zlosynth/proton/eurorack/src/system/randomizer.rs

use hal::prelude::_stm32h7xx_hal_rng_RngCore;
use hal::rng::Rng;
use stm32h7xx_hal as hal;

use proton_instruments_interface::Rand;

pub struct Randomizer {
    pub rng: Rng,
}

impl Randomizer {
    pub fn new(rng: Rng) -> Self {
        Self { rng }
    }
}

impl Rand for Randomizer {
    fn generate(&mut self) -> u16 {
        self.rng.gen().unwrap()
    }
}
