zlosynth/proton/control/src/output_request.rs

#[derive(Clone, Copy, Debug)]
#[cfg_attr(feature = "defmt", derive(defmt::Format))]
pub struct OutputRequest {
    pub gate: [Gate; 3],
    pub cv: [Cv; 2],
}

#[derive(Clone, Copy, Debug)]
#[cfg_attr(feature = "defmt", derive(defmt::Format))]
pub struct Gate {
    pub value: bool,
}

#[derive(Clone, Copy, Debug)]
#[cfg_attr(feature = "defmt", derive(defmt::Format))]
pub struct Cv {
    pub value: f32,
}
