zlosynth/proton/control/src/input_snapshot.rs

#[derive(Clone, Copy, Debug)]
#[cfg_attr(feature = "defmt", derive(defmt::Format))]
pub struct InputSnapshot {
    pub pot: Pot,
    pub cv: [Cv; 5],
}

#[derive(Clone, Copy, Debug)]
#[cfg_attr(feature = "defmt", derive(defmt::Format))]
pub struct Pot {
    pub value: f32,
}

#[derive(Clone, Copy, Debug)]
#[cfg_attr(feature = "defmt", derive(defmt::Format))]
pub struct Cv {
    pub value: f32,
}
