zlosynth/proton/ui/examples/display.rs

use core::fmt;
use std::{thread, time::Duration};

use embedded_graphics::{pixelcolor::BinaryColor, prelude::*};
use embedded_graphics_simulator::{
    sdl2::Keycode, OutputSettingsBuilder, SimulatorDisplay, SimulatorEvent, Window,
};

use proton_ui::action::Action;
use proton_ui::display::*;
use proton_ui::reducer;
use proton_ui::state::*;

fn speed_writter(destination: &mut dyn fmt::Write, value: f32) {
    write!(destination, "{:.2}%", value).unwrap();
}

fn main() -> Result<(), core::convert::Infallible> {
    let mut display: SimulatorDisplay<BinaryColor> =
        SimulatorDisplay::new(Size::new(DISPLAY_WIDTH, DISPLAY_HEIGHT));
    let output_settings = OutputSettingsBuilder::new().scale(2).build();
    let mut window = Window::new("Fonts", &output_settings);

    let mut state = State::new("Proton")
        .with_attributes(&[
            Attribute::new("scale")
                .with_value_select(ValueSelect::new(&["major", "minor"]).unwrap()),
            Attribute::new("root").with_value_select(ValueSelect::new(&["c", "c#"]).unwrap()),
            Attribute::new("speed").with_value_f32(
                ValueF32::new(0.0)
                    .with_min(0.0)
                    .with_max(100.0)
                    .with_step(1.0)
                    .with_writter(speed_writter),
            ),
        ])
        .unwrap();

    let view = (&state).into();
    draw(&mut display, &view)?;
    window.update(&display);

    'running: loop {
        for event in window.events() {
            match event {
                SimulatorEvent::Quit => break 'running Ok(()),
                SimulatorEvent::KeyDown { keycode, .. } => {
                    let action = match keycode {
                        Keycode::Left => Some(Action::EncoderClick),
                        Keycode::Right => Some(Action::EncoderClick),
                        Keycode::Up => Some(Action::EncoderUp),
                        Keycode::Down => Some(Action::EncoderDown),
                        _ => None,
                    };
                    if let Some(action) = action {
                        let reaction = reducer::reduce(action, &mut state);
                        println!("Reaction: {:?}", reaction);
                        let view = (&state).into();
                        draw(&mut display, &view)?;
                    }
                }
                _ => {}
            }
        }

        window.update(&display);

        thread::sleep(Duration::from_millis(50));
    }
}
