zlosynth/proton/ui/src/display.rs

use embedded_graphics::{
    mono_font::{ascii::FONT_6X12, MonoTextStyle},
    pixelcolor::BinaryColor,
    prelude::*,
    primitives::{PrimitiveStyle, Rectangle},
    text::Text,
};

use crate::view::*;

pub const DISPLAY_WIDTH: u32 = 128;
pub const DISPLAY_HEIGHT: u32 = 64;
const HEADER_HEIGHT: u32 = 15;
const HEADER_LINE: u32 = 1;
const ATTRIBUTE_HEIGHT: u32 = 12;
const ATTRIBUTE_PADDING: u32 = 5;
const FONT_WIDTH: u32 = 6;
const FONT_HEIGHT_ABOVE_LINE: u32 = 8;

pub fn draw<D>(target: &mut D, view: &View) -> Result<(), D::Error>
where
    D: DrawTarget<Color = BinaryColor>,
{
    reset_screen(target)?;

    draw_status_bar(target, view.title, view.edit)?;

    for (i, attribute) in view
        .attributes
        .iter()
        .filter_map(|a| a.as_ref())
        .enumerate()
    {
        let highlighted = i == view.selected_attribute;
        draw_attribute(target, attribute, highlighted, i)?;
    }

    Ok(())
}

fn reset_screen<D>(target: &mut D) -> Result<(), D::Error>
where
    D: DrawTarget<Color = BinaryColor>,
{
    draw_rectangle(
        target,
        Point::new(0, 0),
        Size::new(DISPLAY_WIDTH, DISPLAY_HEIGHT),
        BinaryColor::Off,
    )
}

fn draw_status_bar<D>(target: &mut D, text: &str, edit: bool) -> Result<(), D::Error>
where
    D: DrawTarget<Color = BinaryColor>,
{
    draw_rectangle(
        target,
        Point::new(0, HEADER_HEIGHT as i32 - HEADER_LINE as i32),
        Size::new(DISPLAY_WIDTH, HEADER_LINE),
        BinaryColor::On,
    )?;

    let x = x_for_centered_text(text);
    let y = FONT_HEIGHT_ABOVE_LINE as i32;
    draw_text(target, text, Point::new(x, y), BinaryColor::On)?;

    if edit {
        draw_rectangle(
            target,
            Point::new(DISPLAY_WIDTH as i32 - 4, 0),
            Size::new(4, HEADER_HEIGHT),
            BinaryColor::On,
        )?;
    }

    Ok(())
}

fn draw_attribute<D>(
    target: &mut D,
    attribute: &Attribute,
    highlighted: bool,
    position: usize,
) -> Result<(), D::Error>
where
    D: DrawTarget<Color = BinaryColor>,
{
    let (text, background) = if highlighted {
        (BinaryColor::Off, BinaryColor::On)
    } else {
        (BinaryColor::On, BinaryColor::Off)
    };

    let y = position as i32 * ATTRIBUTE_HEIGHT as i32 + HEADER_HEIGHT as i32;

    draw_rectangle(
        target,
        Point::new(0, y),
        Size::new(DISPLAY_WIDTH, ATTRIBUTE_HEIGHT),
        background,
    )?;
    draw_text(
        target,
        attribute.name,
        Point::new(ATTRIBUTE_PADDING as i32, y + FONT_HEIGHT_ABOVE_LINE as i32),
        text,
    )?;

    match &attribute.value {
        Value::Str(value) => {
            let x = x_for_right_justified_text(value);
            draw_text(
                target,
                value,
                Point::new(x, y + FONT_HEIGHT_ABOVE_LINE as i32),
                text,
            )?;
        }
        Value::F32(writter, value) => {
            let mut string = heapless::String::<8>::new();
            writter(&mut string, *value);
            let number = &string;

            let y = y + FONT_HEIGHT_ABOVE_LINE as i32;

            let x = x_for_right_justified_text(number);
            draw_text(target, number, Point::new(x, y), text)?;
        }
    }

    Ok(())
}

fn x_for_right_justified_text(text: &str) -> i32 {
    let text_width = text.len() as i32 * FONT_WIDTH as i32;
    DISPLAY_WIDTH as i32 - text_width - ATTRIBUTE_PADDING as i32
}

fn draw_text<D>(
    target: &mut D,
    text: &str,
    position: Point,
    color: BinaryColor,
) -> Result<(), D::Error>
where
    D: DrawTarget<Color = BinaryColor>,
{
    Text::new(text, position, MonoTextStyle::new(&FONT_6X12, color)).draw(target)?;
    Ok(())
}

fn draw_rectangle<D>(
    target: &mut D,
    start: Point,
    size: Size,
    color: BinaryColor,
) -> Result<(), D::Error>
where
    D: DrawTarget<Color = BinaryColor>,
{
    Rectangle::new(start, size)
        .into_styled(PrimitiveStyle::with_fill(color))
        .draw(target)
}

fn x_for_centered_text(text: &str) -> i32 {
    let text_width = text.len() as i32 * FONT_WIDTH as i32;
    DISPLAY_WIDTH as i32 / 2 - text_width / 2
}
