zlosynth/proton/ui/src/lib.rs

#![no_std]

#[cfg(test)]
#[macro_use]
extern crate approx;

pub mod action;
pub mod display;
pub mod input;
pub mod reaction;
pub mod reducer;
pub mod state;
pub mod view;

// - user input passes actions over a queue to state reducer
// - state reducer keeps State with Vecs etc
// - state reducer passes display state (Copy) via a #[task] argument to display
// - state reducer passes actions via queue to lib front, that handles interporation
// - CV input passes actions via queue to lib front
// - audio loop is owned by the lib itself
